m2415146/Organizer-for-a-drill-parts/STL/PATH for repair box.stl

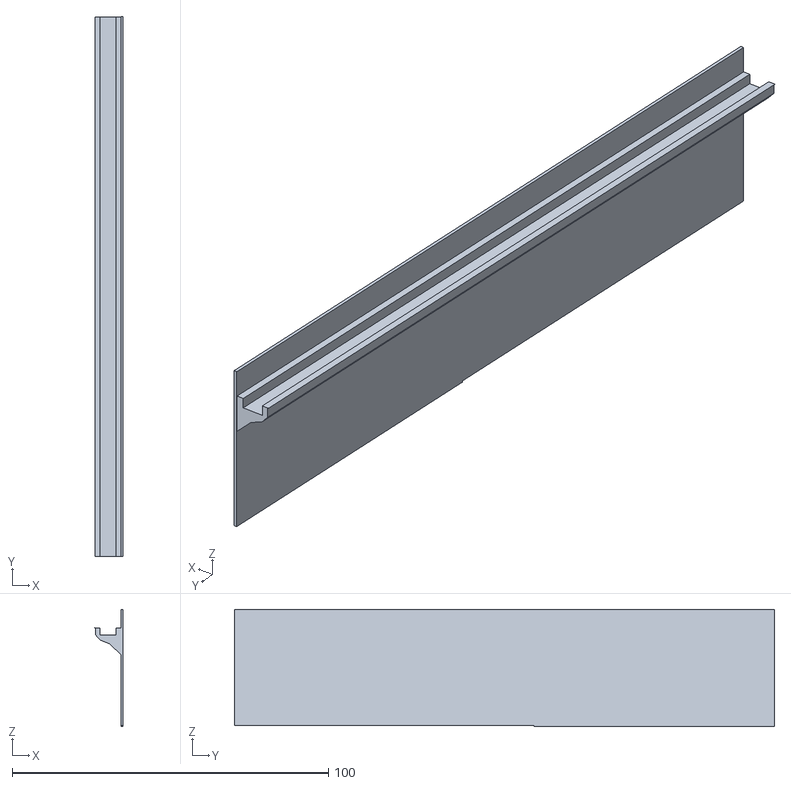
[picture p49: CAD file, 2024-11-26]
STL/PATH for repair box.stl
9.00 x 170.8 x 37.1
