m2415146/Organizer-for-a-drill-parts/dxf/drill for plywood.dxf

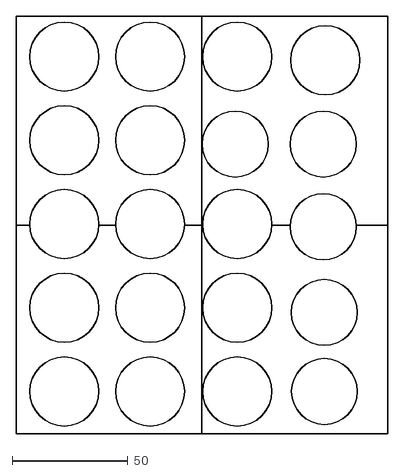
[picture p50: CAD file, 2024-11-26]
dxf/drill for plywood.dxf
160.0 x 180.0
