m2415146/Organizer-for-a-drill-parts/STL/powerline for holder.stl

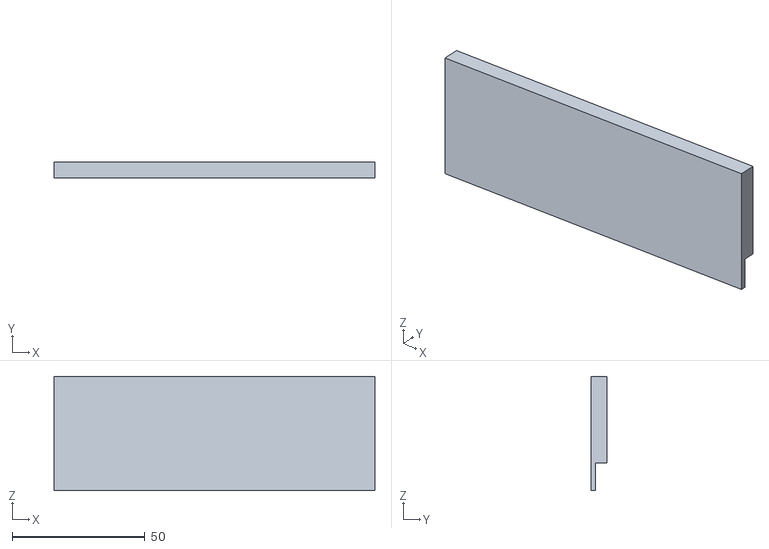
[picture p51: CAD file, 2024-11-26]
STL/powerline for holder.stl
120.7 x 6.03 x 42.9
