m2415146/Organizer-for-a-drill-parts/dxf/Acrylic part true.dxf

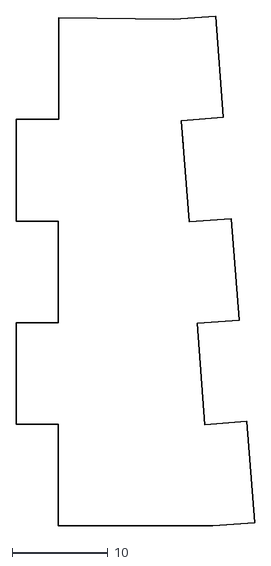
[picture p52: CAD file, 2024-11-26]
dxf/Acrylic part true.dxf
24.9 x 53.2
