m2415146/Organizer-for-a-drill-parts/STL/cap for box.stl

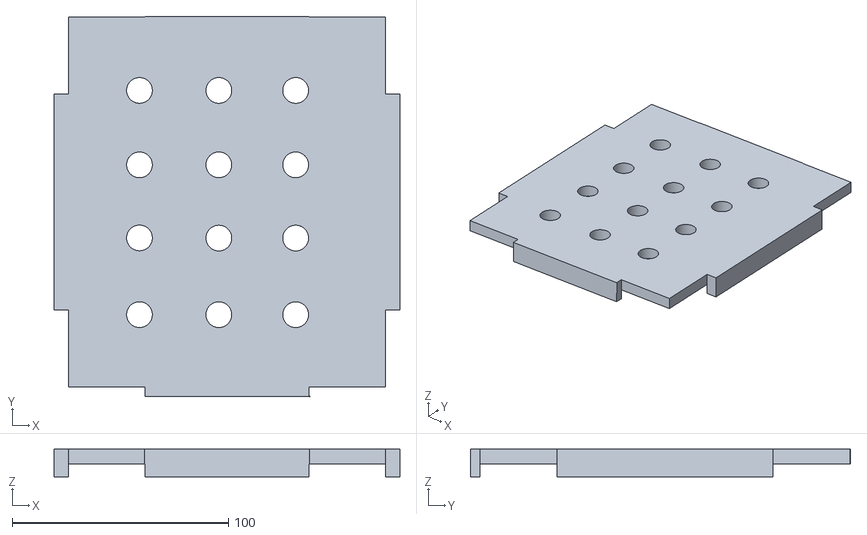
[picture p53: CAD file, 2024-11-18]
STL/cap for box.stl
160.0 x 175.9 x 12.8
